WillWheatley27/EoC-Lab-Camera/main/sd_card_example_main.c

/* SD card and FAT filesystem example.
   This example code is in the Public Domain (or CC0 licensed, at your option.)

   Unless required by applicable law or agreed to in writing, this
   software is distributed on an "AS IS" BASIS, WITHOUT WARRANTIES OR
   CONDITIONS OF ANY KIND, either express or implied.
*/

// This example uses SDMMC peripheral to communicate with SD card.

#include <string.h>
#include <stdio.h>
#include <unistd.h>
#include <errno.h>
#include <sys/stat.h>
#include "driver/i2c.h"
#include "i2c_bus.h"
#include "freertos/FreeRTOS.h"
#include "freertos/task.h"
#include "esp_log.h"
#include "button.h"
#include "ble_trigger.h"
#include "mic_capture.h"
#include "oled_ssd1306.h"
#include "camera_ov2640.h"
#include "tinyusb.h"
#include "tinyusb_default_config.h"
#include "tinyusb_msc.h"
#include "sdmmc_cmd.h"
#include "driver/sdmmc_host.h"
#include "sd_test_io.h"
#if SOC_SDMMC_IO_POWER_EXTERNAL
#include "sd_pwr_ctrl_by_on_chip_ldo.h"
#endif

#define EXAMPLE_MAX_CHAR_SIZE    64

static const char *TAG = "example";

#define MOUNT_POINT "/sdcard"
#define EXAMPLE_IS_UHS1    (CONFIG_EXAMPLE_SDMMC_SPEED_UHS_I_SDR50 || CONFIG_EXAMPLE_SDMMC_SPEED_UHS_I_DDR50)

#define OLED_I2C_SDA       41
#define OLED_I2C_SCL       42
#define I2C_SHARED_FREQ_HZ 100000


#ifdef CONFIG_EXAMPLE_DEBUG_PIN_CONNECTIONS
const char* names[] = {"CLK", "CMD", "D0", "D1", "D2", "D3"};
const int pins[] = {4, 5, 6, 7, 15, 16};

const int pin_count = sizeof(pins)/sizeof(pins[0]);

#if CONFIG_EXAMPLE_ENABLE_ADC_FEATURE
const int adc_channels[] = {CONFIG_EXAMPLE_ADC_PIN_CLK,
                            CONFIG_EXAMPLE_ADC_PIN_CMD,
                            CONFIG_EXAMPLE_ADC_PIN_D0,
                            CONFIG_EXAMPLE_ADC_PIN_D1,
                            CONFIG_EXAMPLE_ADC_PIN_D2,
                            CONFIG_EXAMPLE_ADC_PIN_D3
                            };
#endif //CONFIG_EXAMPLE_ENABLE_ADC_FEATURE

pin_configuration_t config = {
    .names = names,
    .pins = pins,
#if CONFIG_EXAMPLE_ENABLE_ADC_FEATURE
    .adc_channels = adc_channels,
#endif
};
#endif //CONFIG_EXAMPLE_DEBUG_PIN_CONNECTIONS

/* TinyUSB descriptors */
#define EPNUM_MSC            1
#define TUSB_DESC_TOTAL_LEN  (TUD_CONFIG_DESC_LEN + TUD_MSC_DESC_LEN)

enum {
    ITF_NUM_MSC = 0,
    ITF_NUM_TOTAL
};

enum {
    EDPT_CTRL_OUT = 0x00,
    EDPT_CTRL_IN  = 0x80,

    EDPT_MSC_OUT  = 0x01,
    EDPT_MSC_IN   = 0x81,
};

static tusb_desc_device_t descriptor_config = {
    .bLength = sizeof(descriptor_config),
    .bDescriptorType = TUSB_DESC_DEVICE,
    .bcdUSB = 0x0200,
    .bDeviceClass = TUSB_CLASS_MISC,
    .bDeviceSubClass = MISC_SUBCLASS_COMMON,
    .bDeviceProtocol = MISC_PROTOCOL_IAD,
    .bMaxPacketSize0 = CFG_TUD_ENDPOINT0_SIZE,
    .idVendor = 0x303A,
    .idProduct = 0x4002,
    .bcdDevice = 0x100,
    .iManufacturer = 0x01,
    .iProduct = 0x02,
    .iSerialNumber = 0x03,
    .bNumConfigurations = 0x01
};

static uint8_t const msc_fs_configuration_desc[] = {
    TUD_CONFIG_DESCRIPTOR(1, ITF_NUM_TOTAL, 0, TUSB_DESC_TOTAL_LEN, TUSB_DESC_CONFIG_ATT_REMOTE_WAKEUP, 100),
    TUD_MSC_DESCRIPTOR(ITF_NUM_MSC, 0, EDPT_MSC_OUT, EDPT_MSC_IN, 64),
};

#if (TUD_OPT_HIGH_SPEED)
static const tusb_desc_device_qualifier_t device_qualifier = {
    .bLength = sizeof(tusb_desc_device_qualifier_t),
    .bDescriptorType = TUSB_DESC_DEVICE_QUALIFIER,
    .bcdUSB = 0x0200,
    .bDeviceClass = TUSB_CLASS_MISC,
    .bDeviceSubClass = MISC_SUBCLASS_COMMON,
    .bDeviceProtocol = MISC_PROTOCOL_IAD,
    .bMaxPacketSize0 = CFG_TUD_ENDPOINT0_SIZE,
    .bNumConfigurations = 0x01,
    .bReserved = 0
};

static uint8_t const msc_hs_configuration_desc[] = {
    TUD_CONFIG_DESCRIPTOR(1, ITF_NUM_TOTAL, 0, TUSB_DESC_TOTAL_LEN, TUSB_DESC_CONFIG_ATT_REMOTE_WAKEUP, 100),
    TUD_MSC_DESCRIPTOR(ITF_NUM_MSC, 0, EDPT_MSC_OUT, EDPT_MSC_IN, 512),
};
#endif

static char const *string_desc_arr[] = {
    (const char[]) { 0x09, 0x04 },
    "TinyUSB",
    "TinyUSB Device",
    "123456",
};

static tinyusb_msc_storage_handle_t s_storage_hdl;
static tinyusb_config_t s_tusb_cfg;
static bool s_usb_active;

// Writes a test string to a file on the SD card.
static esp_err_t s_example_write_file(const char *path, char *data)
{
    ESP_LOGI(TAG, "Opening file %s", path);
    FILE *f = fopen(path, "w");
    if (f == NULL) {
        ESP_LOGE(TAG, "Failed to open file for writing");
        return ESP_FAIL;
    }
    fprintf(f, data);
    fclose(f);
    ESP_LOGI(TAG, "File written");

    return ESP_OK;
}

// Reads a line from a file on the SD card.
static esp_err_t s_example_read_file(const char *path)
{
    ESP_LOGI(TAG, "Reading file %s", path);
    FILE *f = fopen(path, "r");
    if (f == NULL) {
        ESP_LOGE(TAG, "Failed to open file for reading");
        return ESP_FAIL;
    }
    char line[EXAMPLE_MAX_CHAR_SIZE];
    fgets(line, sizeof(line), f);
    fclose(f);

    // strip newline
    char *pos = strchr(line, '\n');
    if (pos) {
        *pos = '\0';
    }
    ESP_LOGI(TAG, "Read from file: '%s'", line);

    return ESP_OK;
}

// Initializes the SDMMC host/slot and returns a ready card handle.
static esp_err_t s_storage_init_sdmmc(sdmmc_card_t **card)
{
    esp_err_t ret = ESP_OK;
    bool host_init = false;
    sdmmc_card_t *sd_card = NULL;

    sdmmc_host_t host = SDMMC_HOST_DEFAULT();
#if CONFIG_EXAMPLE_SDMMC_SPEED_HS
    host.max_freq_khz = SDMMC_FREQ_HIGHSPEED;
#elif CONFIG_EXAMPLE_SDMMC_SPEED_UHS_I_SDR50
    host.slot = SDMMC_HOST_SLOT_0;
    host.max_freq_khz = SDMMC_FREQ_SDR50;
    host.flags &= ~SDMMC_HOST_FLAG_DDR;
#elif CONFIG_EXAMPLE_SDMMC_SPEED_UHS_I_DDR50
    host.slot = SDMMC_HOST_SLOT_0;
    host.max_freq_khz = SDMMC_FREQ_DDR50;
#endif

#if CONFIG_EXAMPLE_SD_PWR_CTRL_LDO_INTERNAL_IO
    sd_pwr_ctrl_ldo_config_t ldo_config = {
        .ldo_chan_id = CONFIG_EXAMPLE_SD_PWR_CTRL_LDO_IO_ID,
    };
    sd_pwr_ctrl_handle_t pwr_ctrl_handle = NULL;

    ret = sd_pwr_ctrl_new_on_chip_ldo(&ldo_config, &pwr_ctrl_handle);
    if (ret != ESP_OK) {
        ESP_LOGE(TAG, "Failed to create a new on-chip LDO power control driver");
        return ret;
    }
    host.pwr_ctrl_handle = pwr_ctrl_handle;
#endif

    sdmmc_slot_config_t slot_config = SDMMC_SLOT_CONFIG_DEFAULT();
#if EXAMPLE_IS_UHS1
    slot_config.flags |= SDMMC_SLOT_FLAG_UHS1;
#endif
    slot_config.width = 4;

#ifdef CONFIG_SOC_SDMMC_USE_GPIO_MATRIX
    slot_config.clk = 4;
    slot_config.cmd = 5;
    slot_config.d0 = 6;
    slot_config.d1 = 7;
    slot_config.d2 = 15;
    slot_config.d3 = 16;
#endif

    slot_config.flags |= SDMMC_SLOT_FLAG_INTERNAL_PULLUP;

    sd_card = (sdmmc_card_t *)malloc(sizeof(sdmmc_card_t));
    if (!sd_card) {
        return ESP_ERR_NO_MEM;
    }

    ret = (*host.init)();
    if (ret != ESP_OK) {
        goto clean;
    }
    host_init = true;

    ret = sdmmc_host_init_slot(host.slot, (const sdmmc_slot_config_t *)&slot_config);
    if (ret != ESP_OK) {
        goto clean;
    }

    while (sdmmc_card_init(&host, sd_card)) {
        ESP_LOGE(TAG, "Insert uSD card. Retrying...");
        vTaskDelay(pdMS_TO_TICKS(3000));
    }

    sdmmc_card_print_info(stdout, sd_card);
    *card = sd_card;
    return ESP_OK;

clean:
    if (host_init) {
        if (host.flags & SDMMC_HOST_FLAG_DEINIT_ARG) {
            host.deinit_p(host.slot);
        } else {
            (*host.deinit)();
        }
    }
    if (sd_card) {
        free(sd_card);
    }
#if CONFIG_EXAMPLE_SD_PWR_CTRL_LDO_INTERNAL_IO
    sd_pwr_ctrl_del_on_chip_ldo(pwr_ctrl_handle);
#endif
    return ret;
}

static bool s_wait_for_mount(const char *path, int timeout_ms)
{
    struct stat st;
    const int step_ms = 50;
    int waited = 0;
    while (waited < timeout_ms) {
        if (stat(path, &st) == 0) {
            return true;
        }
        vTaskDelay(pdMS_TO_TICKS(step_ms));
        waited += step_ms;
    }
    return false;
}

// Switches TinyUSB MSC mount point between USB and app.
static esp_err_t s_switch_mount(tinyusb_msc_mount_point_t mount_point)
{
    return tinyusb_msc_set_storage_mount_point(s_storage_hdl, mount_point);
}

// Starts the TinyUSB MSC driver if not already running.
static esp_err_t s_usb_start(void)
{
    if (s_usb_active) {
        return ESP_OK;
    }
    esp_err_t ret = tinyusb_driver_install(&s_tusb_cfg);
    if (ret == ESP_OK) {
        s_usb_active = true;
        ESP_LOGI(TAG, "USB MSC ready");
    }
    return ret;
}

// Stops the TinyUSB MSC driver if running.
static void s_usb_stop(void)
{
    if (!s_usb_active) {
        return;
    }
    esp_err_t ret = tinyusb_driver_uninstall();
    if (ret != ESP_OK) {
        ESP_LOGW(TAG, "USB uninstall failed (%s)", esp_err_to_name(ret));
        return;
    }
    s_usb_active = false;
    ESP_LOGI(TAG, "USB MSC stopped");
}


// Initializes peripherals and handles record/USB switching loop.
void app_main(void)
{
    esp_err_t ret;
    camera_app_log_i2c_levels();

    ret = i2c_bus_init(I2C_NUM_1, OLED_I2C_SDA, OLED_I2C_SCL, I2C_SHARED_FREQ_HZ);
    if (ret != ESP_OK) {
        ESP_LOGE(TAG, "I2C init failed (%s)", esp_err_to_name(ret));
        return;
    }

    ESP_LOGI(TAG, "Initializing SD card");
    if (camera_app_init() != ESP_OK) {
        ESP_LOGE(TAG, "Camera disabled");
    }
    if (oled_ssd1306_init() != ESP_OK) {
        ESP_LOGE(TAG, "OLED init failed");
    }
    button_init();
    ble_trigger_init();

    sdmmc_card_t *card = NULL;
    ret = s_storage_init_sdmmc(&card);
    if (ret != ESP_OK) {
        ESP_LOGE(TAG, "Failed to init SD card (%s)", esp_err_to_name(ret));
        return;
    }

    tinyusb_msc_storage_config_t storage_cfg = {
        .mount_point = TINYUSB_MSC_STORAGE_MOUNT_USB,
        .fat_fs = {
            .base_path = MOUNT_POINT,
            .config.max_files = 5,
            .format_flags = 0,
        },
        .medium.card = card,
    };

    ESP_ERROR_CHECK(tinyusb_msc_new_storage_sdmmc(&storage_cfg, &s_storage_hdl));

    s_tusb_cfg = (tinyusb_config_t)TINYUSB_DEFAULT_CONFIG();
    s_tusb_cfg.descriptor.device = &descriptor_config;
    s_tusb_cfg.descriptor.full_speed_config = msc_fs_configuration_desc;
    s_tusb_cfg.descriptor.string = string_desc_arr;
    s_tusb_cfg.descriptor.string_count = sizeof(string_desc_arr) / sizeof(string_desc_arr[0]);
#if (TUD_OPT_HIGH_SPEED)
    s_tusb_cfg.descriptor.high_speed_config = msc_hs_configuration_desc;
    s_tusb_cfg.descriptor.qualifier = &device_qualifier;
#endif

    ESP_ERROR_CHECK(s_usb_start());
    ESP_LOGI(TAG, "Exposing SD card over USB");
    ESP_ERROR_CHECK(s_switch_mount(TINYUSB_MSC_STORAGE_MOUNT_USB));

    uint32_t file_index = 1;
    while (true) {
        while (!button_is_recording()) {
            vTaskDelay(pdMS_TO_TICKS(50));
        }

        ESP_LOGI(TAG, "Disabling USB and mounting SD card for recording");
        s_usb_stop();
        ret = s_switch_mount(TINYUSB_MSC_STORAGE_MOUNT_APP);
        if (ret != ESP_OK) {
            ESP_LOGE(TAG, "Failed to mount to app (%s)", esp_err_to_name(ret));
            vTaskDelay(pdMS_TO_TICKS(1000));
            continue;
        }

        char mic_path[EXAMPLE_MAX_CHAR_SIZE];
        char video_path[EXAMPLE_MAX_CHAR_SIZE];
        char timestamp[16];
        bool use_index_name = true;
        if (ble_trigger_get_timestamp(timestamp, sizeof(timestamp))) {
            // 8.3-safe names using YYMMDDHH (hour resolution) for both media types.
            snprintf(mic_path, sizeof(mic_path), MOUNT_POINT"/%s.WAV", timestamp);
            snprintf(video_path, sizeof(video_path), MOUNT_POINT"/%s.MJP", timestamp);
            use_index_name = false;
        } else {
            snprintf(mic_path, sizeof(mic_path), MOUNT_POINT"/mic_%04u.wav", (unsigned)file_index);
            // Use 8.3-compatible name to avoid FATFS EINVAL when LFN is disabled.
            snprintf(video_path, sizeof(video_path), MOUNT_POINT"/VID%04u.MJP", (unsigned)file_index);
        }

        if (!s_wait_for_mount(MOUNT_POINT, 2000)) {
            ESP_LOGE(TAG, "Mount not ready for %s", MOUNT_POINT);
        }

        if (camera_app_is_ready() && !camera_app_is_recording()) {
            esp_err_t cam_ret = camera_app_start_record(video_path);
            if (cam_ret != ESP_OK && !use_index_name) {
                ESP_LOGW(TAG, "Timestamped video name failed (%s); using index", esp_err_to_name(cam_ret));
                snprintf(video_path, sizeof(video_path), MOUNT_POINT"/VID%04u.MJP", (unsigned)file_index);
                use_index_name = true;
                camera_app_start_record(video_path);
            }
        }
        int captured_seconds = 0;
        ret = mic_capture_start(mic_path, 0);
        if (ret != ESP_OK) {
            if (!use_index_name) {
                ESP_LOGW(TAG, "Timestamped mic name failed (%s); using index", esp_err_to_name(ret));
                snprintf(mic_path, sizeof(mic_path), MOUNT_POINT"/mic_%04u.wav", (unsigned)file_index);
                use_index_name = true;
                ret = mic_capture_start(mic_path, 0);
            }
            if (ret != ESP_OK) {
                ESP_LOGE(TAG, "Mic capture start failed");
            }
        } else {
            ret = mic_capture_wait(&captured_seconds, portMAX_DELAY);
            if (ret != ESP_OK) {
                ESP_LOGE(TAG, "Mic capture failed");
            } else {
                char line1[32];
                const char *filename = strrchr(mic_path, '/');
                if (filename != NULL) {
                    filename++;
                } else {
                    filename = mic_path;
                }
                snprintf(line1, sizeof(line1), "Recorded %ds at", captured_seconds);
                button_set_idle_display(line1, filename);
                if (use_index_name) {
                    file_index++;
                }
            }
        }

        ESP_LOGI(TAG, "Exposing SD card over USB");
        camera_app_wait_for_stop();
        ESP_ERROR_CHECK(s_switch_mount(TINYUSB_MSC_STORAGE_MOUNT_USB));
        ESP_ERROR_CHECK(s_usb_start());
    }
}
